secersh/etzee/hardware/b11/mcad/pcb-outlines/common/ETZ-B11-DSP.dxf

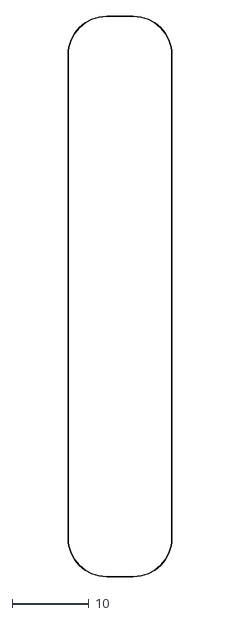
[picture p16: CAD file, 2026-06-08]
hardware/b11/mcad/pcb-outlines/common/ETZ-B11-DSP.dxf
13.5 x 72.8
