secersh/etzee/hardware/b11/mcad/pcb-outlines/MX/ETZ-B11-LSP-5-MX.dxf

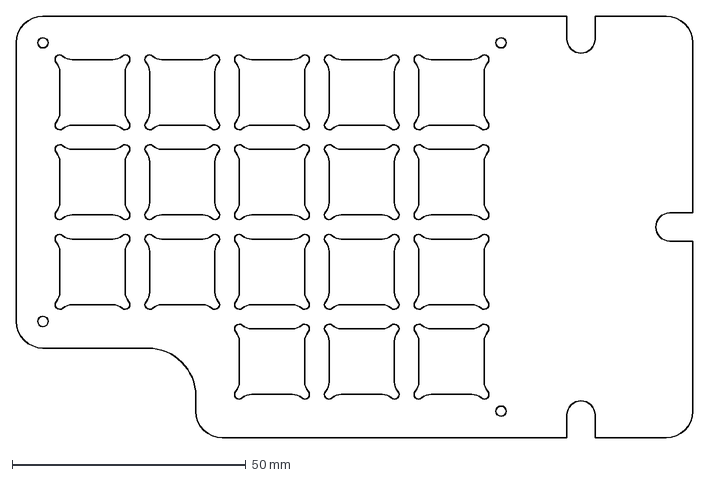
[picture p17: CAD file, 2026-05-23]
hardware/b11/mcad/pcb-outlines/MX/ETZ-B11-LSP-5-MX.dxf
144.7 x 90.2 mm
