secersh/etzee/hardware/b11/mcad/pcb-outlines/CHOC-V2/ETZ-B11-LSC-5-CHOC-V2.dxf

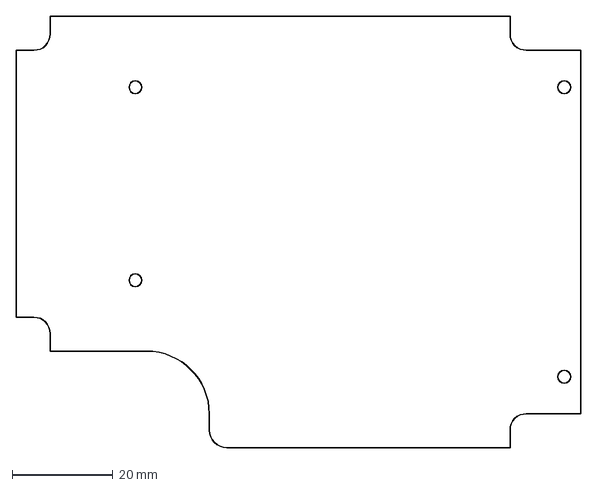
[picture p18: CAD file, 2026-05-23]
hardware/b11/mcad/pcb-outlines/CHOC-V2/ETZ-B11-LSC-5-CHOC-V2.dxf
112.3 x 85.8 mm
