secersh/etzee/hardware/b11/mcad/pcb-outlines/MX/ETZ-B11-LSC-5-MX.dxf

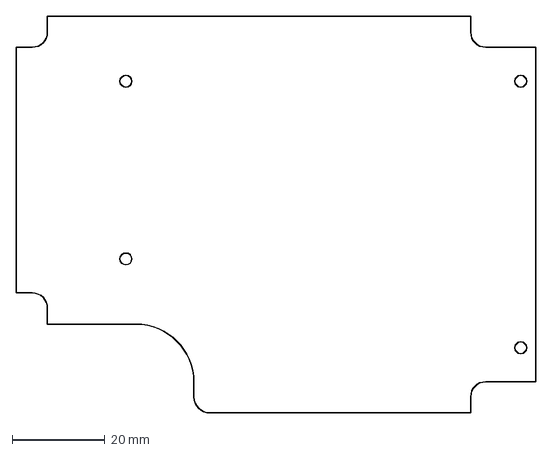
[picture p19: CAD file, 2026-05-23]
hardware/b11/mcad/pcb-outlines/MX/ETZ-B11-LSC-5-MX.dxf
112.3 x 85.8 mm
