secersh/etzee/hardware/b11/ecad/common/ETZ-B11-DSP.kicad_pcb

## KiCad design hardware/b11/ecad/common/ETZ-B11-DSP.kicad_pcb (2026-06-08)

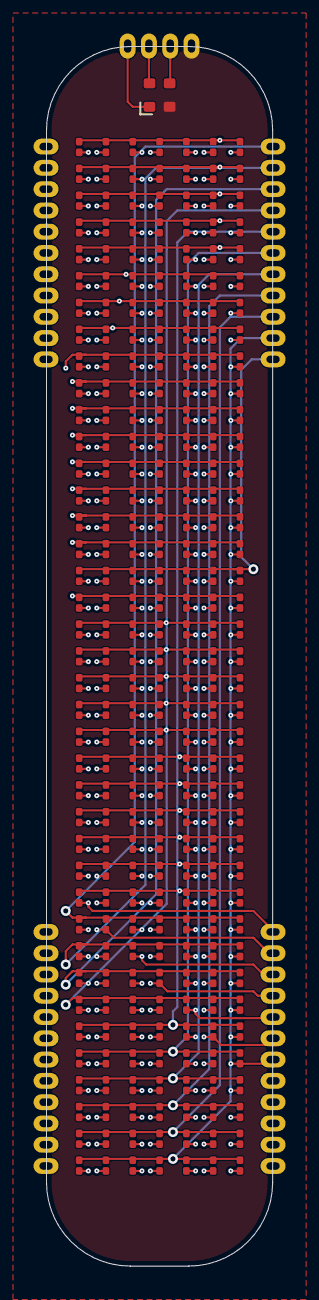
[picture p24: board ETZ-B11-DSP.kicad_pcb from above]

Board: 4 copper layers, 13.5 x 72.8 mm, 276 parts (0 on the bottom side), 50 nets.

Parts:
D1, D2, D3, D4, D5, D6, D7, D8, D9, D10, D11, D12, D13, D14, D15, D16, D17, D18, D19, D20, D21, D22, D23, D24, D25, D26, D27, D28, D29, D30, D31, D32, D33, D34, D35, D36, D37, D38, D39, D40, D41, D42, D43, D44, D45, D46, D47, D48, D49, D50, D51, D52, D53, D54, D55, D56, D57, D58, D59, D60, D61, D62, D63, D64, D65, D66, D67, D68, D69, D70, D71, D72, D73, D74, D75, D76, D77, D78, D79, D80, D81, D82, D83, D84, D85, D86, D87, D88, D89, D90, D91, D92, D93, D94, D95, D96, D97, D98, D99, D100, D101, D102, D103, D104, D105, D106, D107, D108, D109, D110, D111, D112, D113, D114, D115, D116, D117, D118, D119, D120, D121, D122, D123, D124, D125, D126, D127, D128, D129, D130, D131, D132, D133, D134, D135, D136, D137, D138, D139, D140, D141, D142, D143, D144, D145, D146, D147, D148, D149, D150, D151, D152, D153, D154, D155, D156, D157, D158, D159, D160, D161, D162, D163, D164, D165, D166, D167, D168, D169, D170, D171, D172, D173, D174, D175, D176, D177, D178, D179, D180, D181, D182, D183, D184, D185, D186, D187, D188, D189, D190, D191, D192, D193, D194, D195, D196, D197, D198, D199, D200, D201, D202, D203, D204, D205, D206, D207, D208, D209, D210, D211, D212, D213, D214, D215, D216, D217, D218, D219, D220, D221, D222, D223, D224, D225, D226, D227, D228, D229, D230, D231, D232, D233, D234, D235, D236, D237, D238, D239, D240, D241, D242, D243, D244, D245, D246, D247, D248, D249, D250, D251, D252, D253, D254, D255, D256, D257, D258, D259, D260, D261, D262, D263, D264, D265, D266, D267, D268, D269, D270, D271, D272, D273: 0201_LED
J1: DSP_LED_CASTELLATIONS
J_ALS1: DSP_ALS_CASTELLATIONS
U_ALS1: LTR-329ALS-01

Connections:
ALS_GND: J_ALS1.4, U_ALS1.2
ALS_SCL: J_ALS1.2, U_ALS1.4
ALS_SDA: J_ALS1.3, U_ALS1.3
ALS_VDD: J_ALS1.1, U_ALS1.1
LED_CS1: D1.1, D2.1, D3.1, D4.1, D5.1, D6.1, D7.1, J1.28
LED_CS2: D8.1, D9.1, D10.1, D11.1, D12.1, D13.1, D14.1, J1.27
LED_CS3: D15.1, D16.1, D17.1, D18.1, D19.1, D20.1, D21.1, J1.26
LED_CS4: D22.1, D23.1, D24.1, D25.1, D26.1, D27.1, D28.1, J1.25
LED_CS5: D29.1, D30.1, D31.1, D32.1, D33.1, D34.1, D35.1, J1.24
LED_CS6: D36.1, D37.1, D38.1, D39.1, D40.1, D41.1, D42.1, J1.23
LED_CS7: D43.1, D44.1, D45.1, D46.1, D47.1, D48.1, D49.1, J1.22
LED_CS8: D50.1, D51.1, D52.1, D53.1, D54.1, D55.1, D56.1, J1.21
LED_CS9: D57.1, D58.1, D59.1, D60.1, D61.1, D62.1, D63.1, J1.20
LED_CS10: D64.1, D65.1, D66.1, D67.1, D68.1, D69.1, D70.1, J1.19
LED_CS11: D71.1, D72.1, D73.1, D74.1, D75.1, D76.1, D77.1, J1.18
LED_CS12: D78.1, D79.1, D80.1, D81.1, D82.1, D83.1, D84.1, J1.17
LED_CS13: D85.1, D86.1, D87.1, D88.1, D89.1, D90.1, D91.1, J1.16
LED_CS14: D92.1, D93.1, D94.1, D95.1, D96.1, D97.1, D98.1, J1.15
LED_CS15: D99.1, D100.1, D101.1, D102.1, D103.1, D104.1, D105.1, J1.14
LED_CS16: D106.1, D107.1, D108.1, D109.1, D110.1, D111.1, D112.1, J1.13
LED_CS17: D113.1, D114.1, D115.1, D116.1, D117.1, D118.1, D119.1, J1.36
LED_CS18: D120.1, D121.1, D122.1, D123.1, D124.1, D125.1, D126.1, J1.12
LED_CS19: D127.1, D128.1, D129.1, D130.1, D131.1, D132.1, D133.1, J1.11
LED_CS20: D134.1, D135.1, D136.1, D137.1, D138.1, D139.1, D140.1, J1.10
LED_CS21: D141.1, D142.1, D143.1, D144.1, D145.1, D146.1, D147.1, J1.9
LED_CS22: D148.1, D149.1, D150.1, D151.1, D152.1, D153.1, D154.1, J1.8
LED_CS23: D155.1, D156.1, D157.1, D158.1, D159.1, D160.1, D161.1, J1.7
LED_CS24: D162.1, D163.1, D164.1, D165.1, D166.1, D167.1, D168.1, J1.6
LED_CS25: D169.1, D170.1, D171.1, D172.1, D173.1, D174.1, D175.1, J1.5
LED_CS26: D176.1, D177.1, D178.1, D179.1, D180.1, D181.1, D182.1, J1.4
LED_CS27: D183.1, D184.1, D185.1, D186.1, D187.1, D188.1, D189.1, J1.3
LED_CS28: D190.1, D191.1, D192.1, D193.1, D194.1, D195.1, D196.1, J1.2
LED_CS29: D197.1, D198.1, D199.1, D200.1, D201.1, D202.1, D203.1, J1.1
LED_CS30: D204.1, D205.1, D206.1, D207.1, D208.1, D209.1, D210.1, J1.46
LED_CS31: D211.1, D212.1, D213.1, D214.1, D215.1, D216.1, D217.1, J1.45
LED_CS32: D218.1, D219.1, D220.1, D221.1, D222.1, D223.1, D224.1, J1.44
LED_CS33: D225.1, D226.1, D227.1, D228.1, D229.1, D230.1, D231.1, J1.43
LED_CS34: D232.1, D233.1, D234.1, D235.1, D236.1, D237.1, D238.1, J1.42
LED_CS35: D239.1, D240.1, D241.1, D242.1, D243.1, D244.1, D245.1, J1.41
LED_CS36: D246.1, D247.1, D248.1, D249.1, D250.1, D251.1, D252.1, J1.40
LED_CS37: D253.1, D254.1, D255.1, D256.1, D257.1, D258.1, D259.1, J1.39
LED_CS38: D260.1, D261.1, D262.1, D263.1, D264.1, D265.1, D266.1, J1.38
LED_CS39: D267.1, D268.1, D269.1, D270.1, D271.1, D272.1, D273.1, J1.37
LED_SW1: D1.2, D8.2, D15.2, D22.2, D29.2, D36.2, D43.2, D50.2, D57.2, D64.2, D71.2, D78.2, D85.2, D92.2, D99.2, D106.2, D113.2, D120.2, D127.2, D134.2, D141.2, D148.2, D155.2, D162.2, D169.2, D176.2, D183.2, D190.2, D197.2, D204.2, D211.2, D218.2, D225.2, D232.2, D239.2, D246.2, D253.2, D260.2, D267.2, J1.35
LED_SW2: D2.2, D9.2, D16.2, D23.2, D30.2, D37.2, D44.2, D51.2, D58.2, D65.2, D72.2, D79.2, D86.2, D93.2, D100.2, D107.2, D114.2, D121.2, D128.2, D135.2, D142.2, D149.2, D156.2, D163.2, D170.2, D177.2, D184.2, D191.2, D198.2, D205.2, D212.2, D219.2, D226.2, D233.2, D240.2, D247.2, D254.2, D261.2, D268.2, J1.34
LED_SW3: D3.2, D10.2, D17.2, D24.2, D31.2, D38.2, D45.2, D52.2, D59.2, D66.2, D73.2, D80.2, D87.2, D94.2, D101.2, D108.2, D115.2, D122.2, D129.2, D136.2, D143.2, D150.2, D157.2, D164.2, D171.2, D178.2, D185.2, D192.2, D199.2, D206.2, D213.2, D220.2, D227.2, D234.2, D241.2, D248.2, D255.2, D262.2, D269.2, J1.33
LED_SW4: D4.2, D11.2, D18.2, D25.2, D32.2, D39.2, D46.2, D53.2, D60.2, D67.2, D74.2, D81.2, D88.2, D95.2, D102.2, D109.2, D116.2, D123.2, D130.2, D137.2, D144.2, D151.2, D158.2, D165.2, D172.2, D179.2, D186.2, D193.2, D200.2, D207.2, D214.2, D221.2, D228.2, D235.2, D242.2, D249.2, D256.2, D263.2, D270.2, J1.32
LED_SW5: D5.2, D12.2, D19.2, D26.2, D33.2, D40.2, D47.2, D54.2, D61.2, D68.2, D75.2, D82.2, D89.2, D96.2, D103.2, D110.2, D117.2, D124.2, D131.2, D138.2, D145.2, D152.2, D159.2, D166.2, D173.2, D180.2, D187.2, D194.2, D201.2, D208.2, D215.2, D222.2, D229.2, D236.2, D243.2, D250.2, D257.2, D264.2, D271.2, J1.31
LED_SW6: D6.2, D13.2, D20.2, D27.2, D34.2, D41.2, D48.2, D55.2, D62.2, D69.2, D76.2, D83.2, D90.2, D97.2, D104.2, D111.2, D118.2, D125.2, D132.2, D139.2, D146.2, D153.2, D160.2, D167.2, D174.2, D181.2, D188.2, D195.2, D202.2, D209.2, D216.2, D223.2, D230.2, D237.2, D244.2, D251.2, D258.2, D265.2, D272.2, J1.30
LED_SW7: D7.2, D14.2, D21.2, D28.2, D35.2, D42.2, D49.2, D56.2, D63.2, D70.2, D77.2, D84.2, D91.2, D98.2, D105.2, D112.2, D119.2, D126.2, D133.2, D140.2, D147.2, D154.2, D161.2, D168.2, D175.2, D182.2, D189.2, D196.2, D203.2, D210.2, D217.2, D224.2, D231.2, D238.2, D245.2, D252.2, D259.2, D266.2, D273.2, J1.29
